NRS048/ArenaTimer/Print Files and Cad/Housing/Large Printer/Lenses/bottom_right.stl

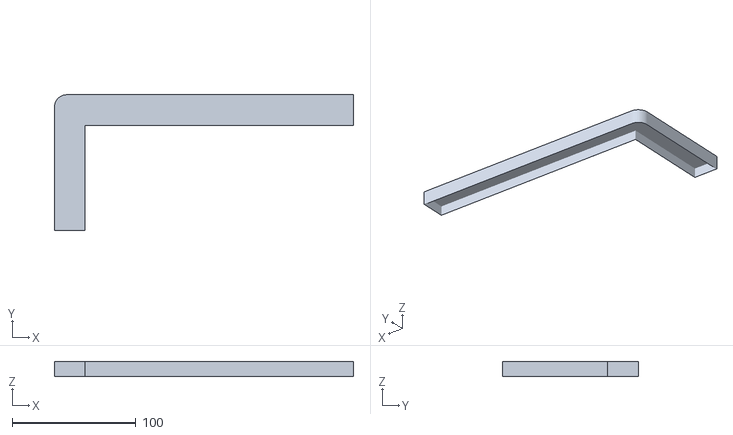
[picture p19: CAD file, 2026-07-04]
Print Files and Cad/Housing/Large Printer/Lenses/bottom_right.stl
242.1 x 109.8 x 12.5
