NRS048/ArenaTimer/Print Files and Cad/Housing/Small Printer/Bottom_right.stl

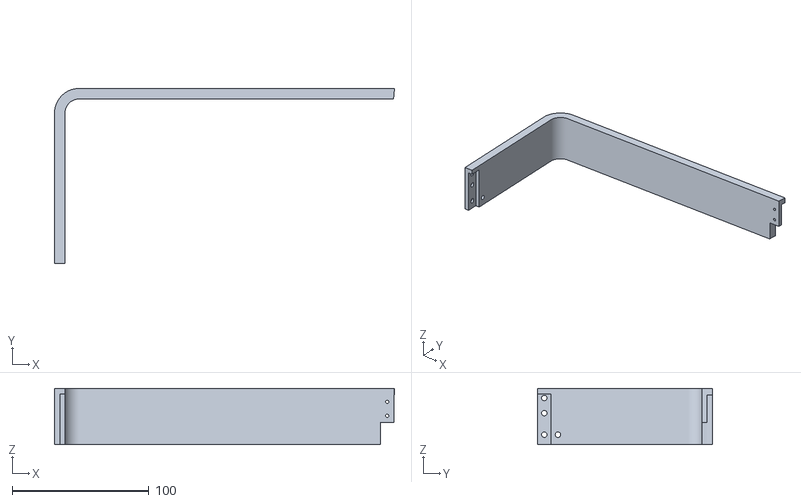
[picture p20: CAD file, 2026-07-04]
Print Files and Cad/Housing/Small Printer/Bottom_right.stl
248.6 x 128.0 x 41.0
