NRS048/ArenaTimer/Print Files and Cad/Remotes/Driver Ready/Driver Ready Remote v2_Driver Ready Remote v2_Body34.stl

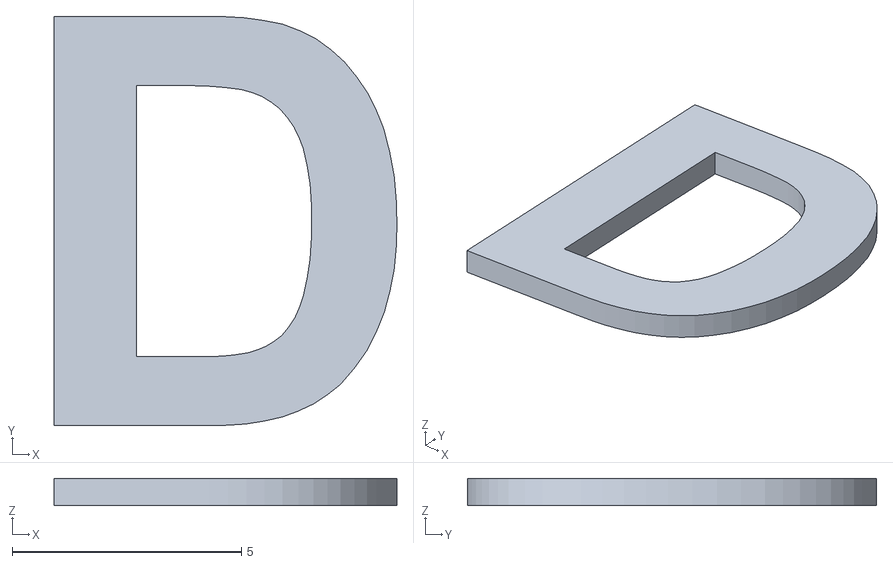
[picture p21: CAD file, 2026-07-04]
Print Files and Cad/Remotes/Driver Ready/Driver Ready Remote v2_Driver Ready Remote v2_Body34.stl
7.48 x 8.93 x 0.6
