NRS048/ArenaTimer/Print Files and Cad/Housing/Small Printer/Bottom_left.stl

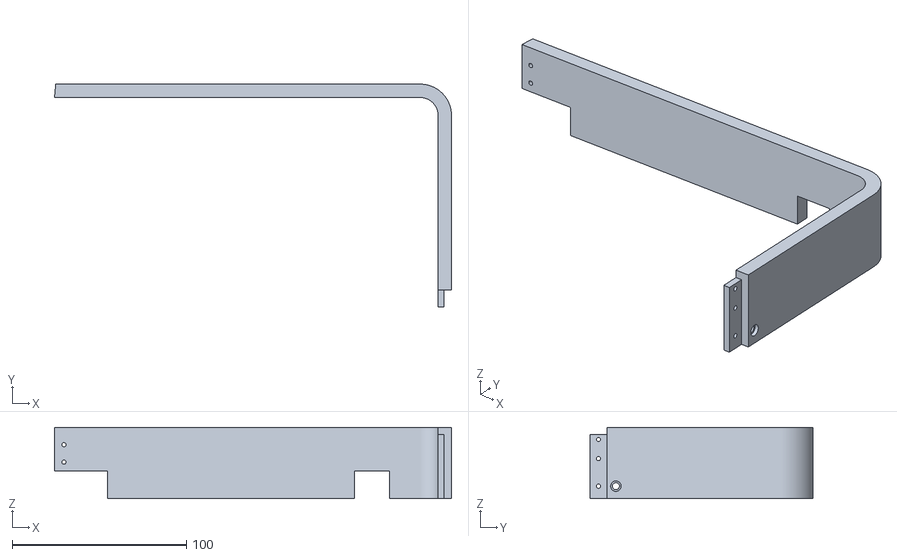
[picture p22: CAD file, 2026-07-04]
Print Files and Cad/Housing/Small Printer/Bottom_left.stl
227.7 x 127.8 x 41.0
