NRS048/ArenaTimer/Print Files and Cad/Housing/Small Printer/Lenses/seg_b.stl

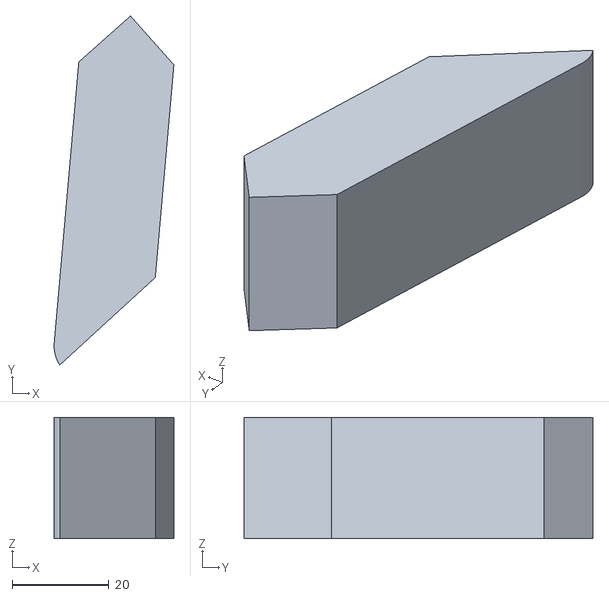
[picture p23: CAD file, 2026-07-04]
Print Files and Cad/Housing/Small Printer/Lenses/seg_b.stl
24.7 x 72.0 x 25.0
