NRS048/ArenaTimer/Print Files and Cad/Remotes/Driver Ready/Driver Ready Remote v2_Driver Ready Remote v2_Body25.stl

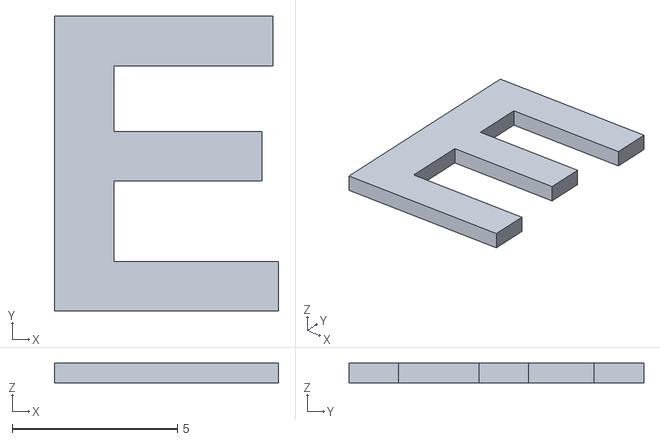
[picture p24: CAD file, 2026-07-04]
Print Files and Cad/Remotes/Driver Ready/Driver Ready Remote v2_Driver Ready Remote v2_Body25.stl
6.79 x 8.93 x 0.6
