NRS048/ArenaTimer/Print Files and Cad/Housing/Small Printer/Lenses/Top_right_lens.stl

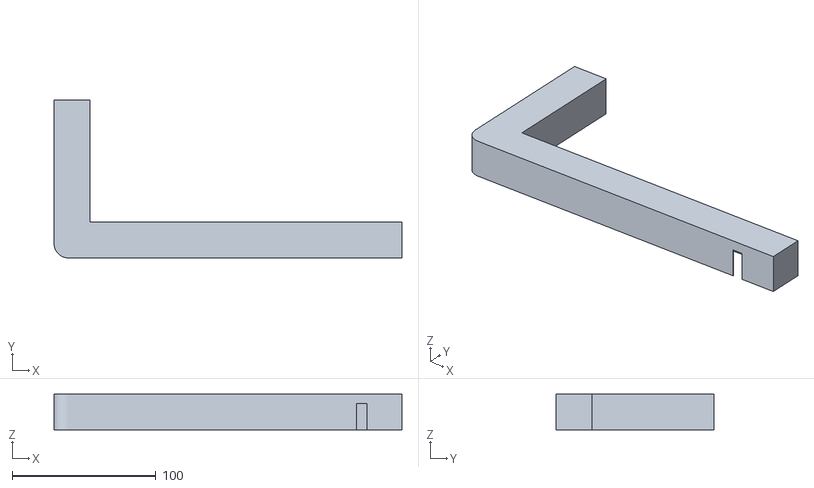
[picture p25: CAD file, 2026-07-04]
Print Files and Cad/Housing/Small Printer/Lenses/Top_right_lens.stl
242.2 x 109.9 x 25.0
