NRS048/ArenaTimer/Print Files and Cad/Housing/Small Printer/Top_left.stl

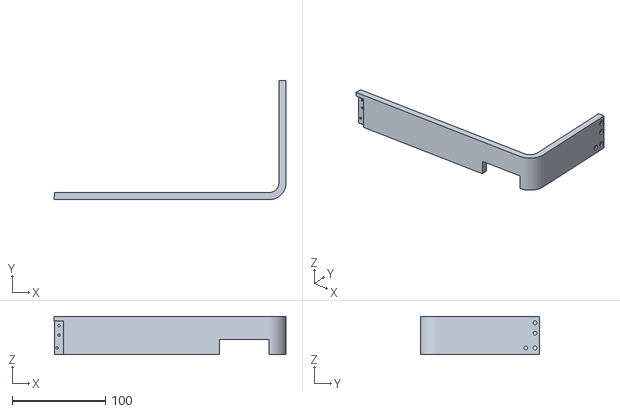
[picture p26: CAD file, 2026-07-04]
Print Files and Cad/Housing/Small Printer/Top_left.stl
248.6 x 128.0 x 41.0
