NRS048/ArenaTimer/Print Files and Cad/Remotes/Driver Ready/Driver Ready Remote v2_Driver Ready Remote v2_Body20.stl

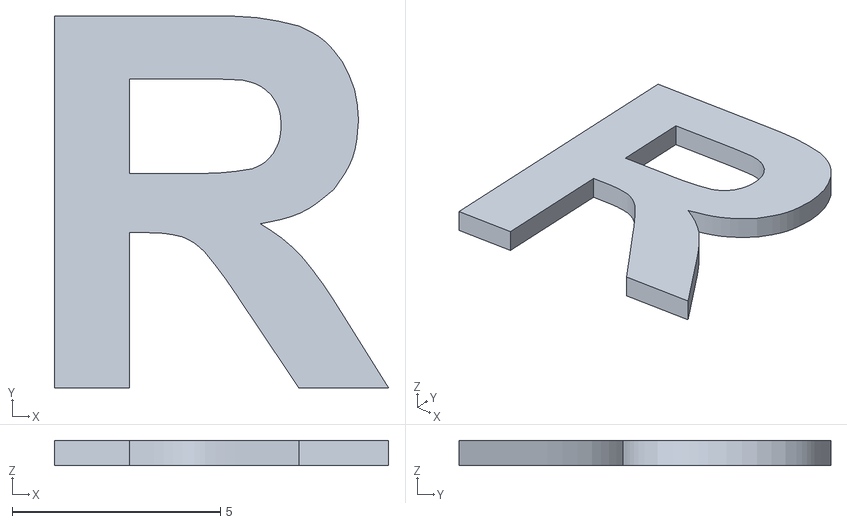
[picture p28: CAD file, 2026-07-04]
Print Files and Cad/Remotes/Driver Ready/Driver Ready Remote v2_Driver Ready Remote v2_Body20.stl
8.03 x 8.93 x 0.6
