NRS048/ArenaTimer/Print Files and Cad/Housing/Large Printer/Lenses/seg_f.stl

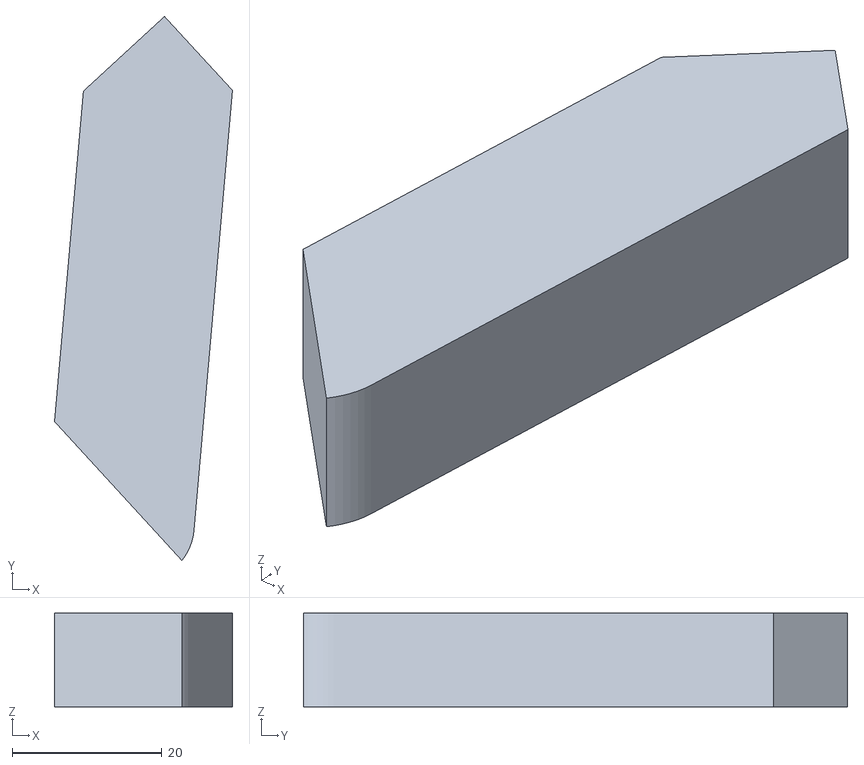
[picture p29: CAD file, 2026-07-04]
Print Files and Cad/Housing/Large Printer/Lenses/seg_f.stl
23.7 x 72.6 x 12.5
