NRS048/ArenaTimer/Print Files and Cad/Housing/Small Printer/Lenses/seg_g.stl

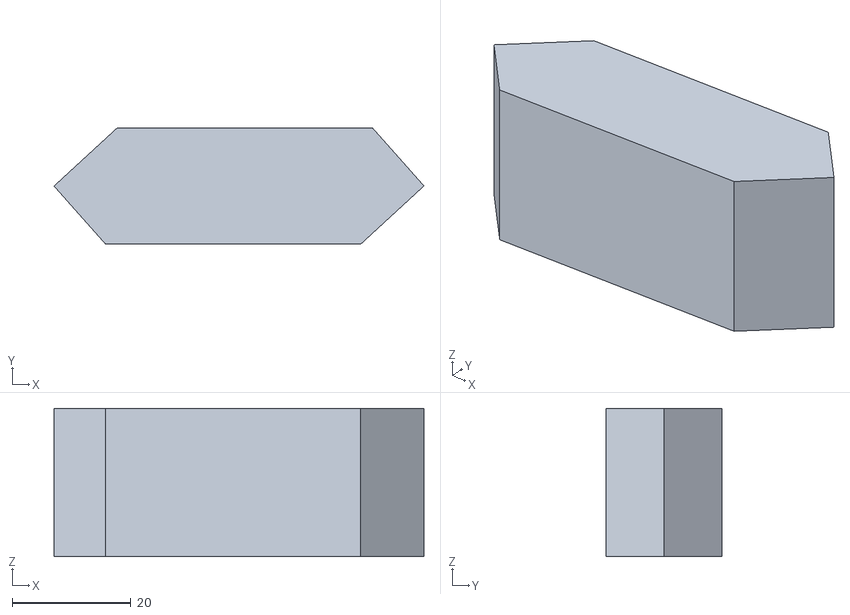
[picture p30: CAD file, 2026-07-04]
Print Files and Cad/Housing/Small Printer/Lenses/seg_g.stl
62.4 x 19.6 x 25.0
