NRS048/ArenaTimer/Print Files and Cad/Remotes/Controller/Timer Remote v22_Timer Remote v22_Body34.stl

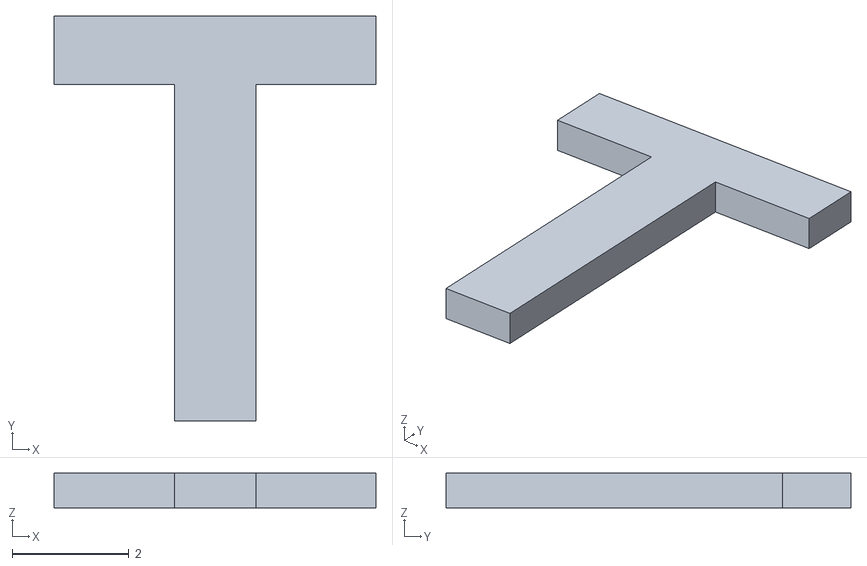
[picture p31: CAD file, 2026-07-20]
Print Files and Cad/Remotes/Controller/Timer Remote v22_Timer Remote v22_Body34.stl
5.52 x 6.94 x 0.6
