NRS048/ArenaTimer/Print Files and Cad/Remotes/Driver Ready/Driver Ready Remote v2_Driver Ready Remote v2_housing.stl

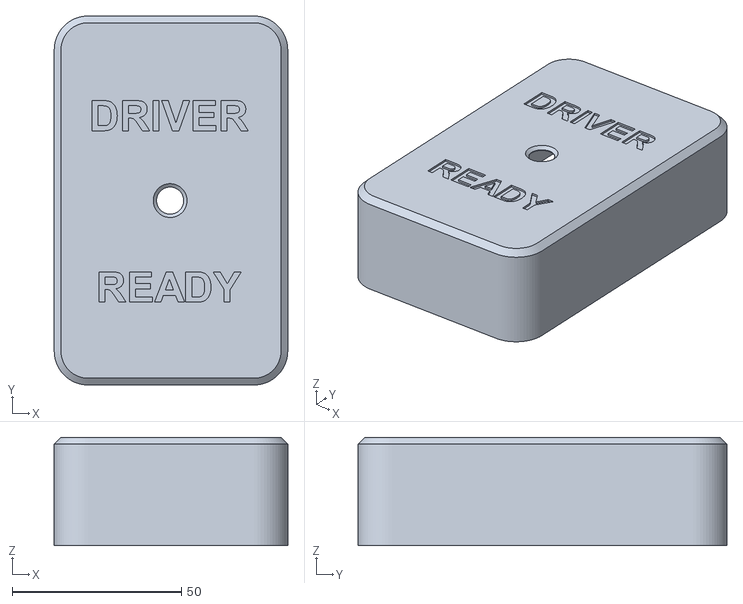
[picture p32: CAD file, 2026-07-04]
Print Files and Cad/Remotes/Driver Ready/Driver Ready Remote v2_Driver Ready Remote v2_housing.stl
69.0 x 109.0 x 32.0
