NRS048/ArenaTimer/Print Files and Cad/Housing/Small Printer/Lenses/seg_f.stl

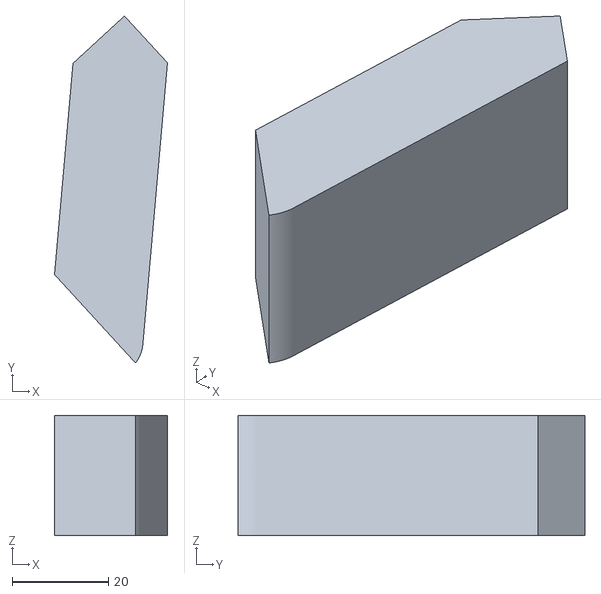
[picture p34: CAD file, 2026-07-04]
Print Files and Cad/Housing/Small Printer/Lenses/seg_f.stl
23.5 x 72.3 x 25.0
