NRS048/ArenaTimer/Print Files and Cad/Remotes/Controller/Timer Remote v22_Timer Remote v22_Body25.stl

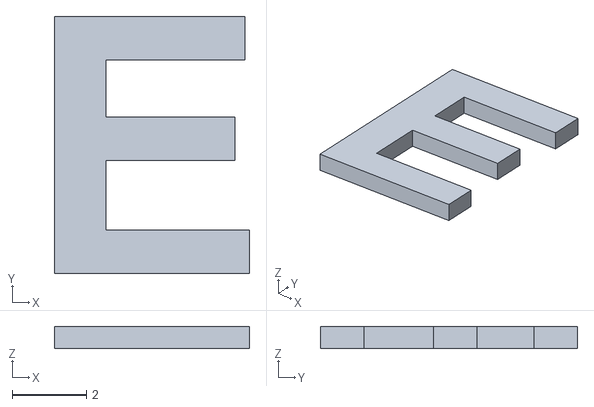
[picture p35: CAD file, 2026-07-20]
Print Files and Cad/Remotes/Controller/Timer Remote v22_Timer Remote v22_Body25.stl
5.28 x 6.94 x 0.6
