NRS048/ArenaTimer/Print Files and Cad/Housing/Large Printer/Lenses/seg_g.stl

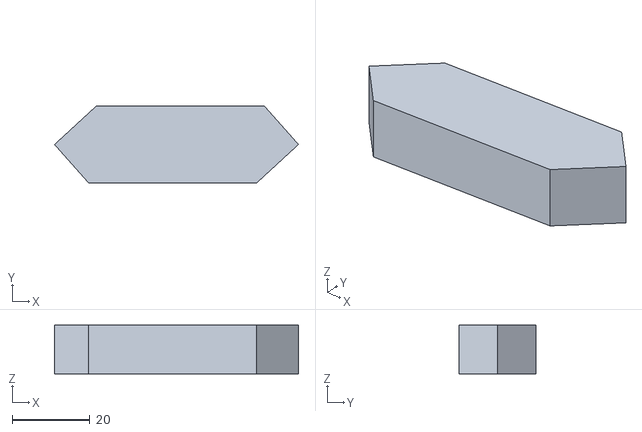
[picture p37: CAD file, 2026-07-04]
Print Files and Cad/Housing/Large Printer/Lenses/seg_g.stl
62.6 x 19.8 x 12.5
