NRS048/ArenaTimer/Print Files and Cad/Remotes/Controller/Timer Remote v22_Timer Remote v22_Body11.stl

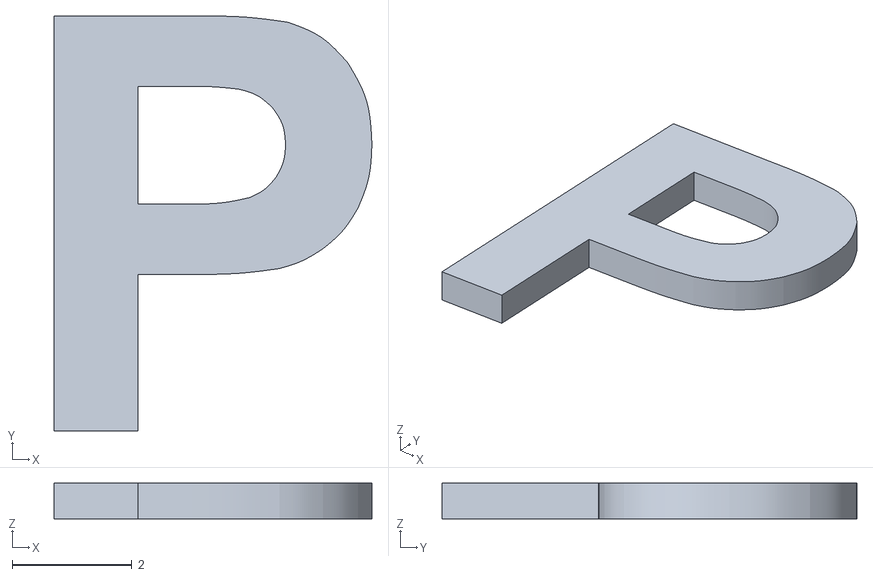
[picture p38: CAD file, 2026-07-20]
Print Files and Cad/Remotes/Controller/Timer Remote v22_Timer Remote v22_Body11.stl
5.32 x 6.94 x 0.6
