NRS048/ArenaTimer/Print Files and Cad/Remotes/Controller/Timer Remote v22_Timer Remote v22_Body26.stl

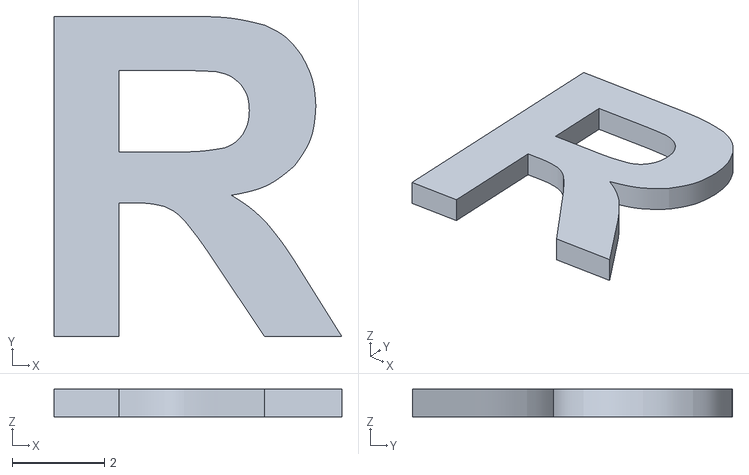
[picture p39: CAD file, 2026-07-20]
Print Files and Cad/Remotes/Controller/Timer Remote v22_Timer Remote v22_Body26.stl
6.24 x 6.94 x 0.6
