NRS048/ArenaTimer/Print Files and Cad/Housing/Small Printer/Lenses/seg_e.stl

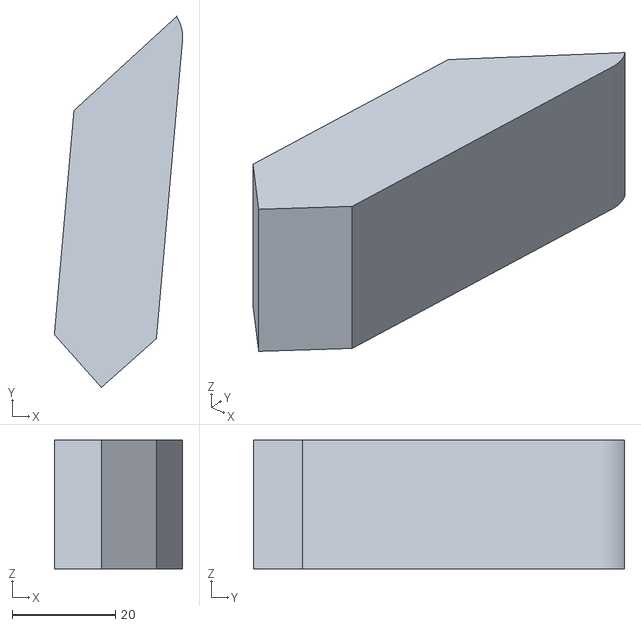
[picture p40: CAD file, 2026-07-04]
Print Files and Cad/Housing/Small Printer/Lenses/seg_e.stl
24.9 x 72.0 x 25.0
