NRS048/ArenaTimer/Print Files and Cad/Remotes/Controller/Timer Remote v22_Timer Remote v22_Body10.stl

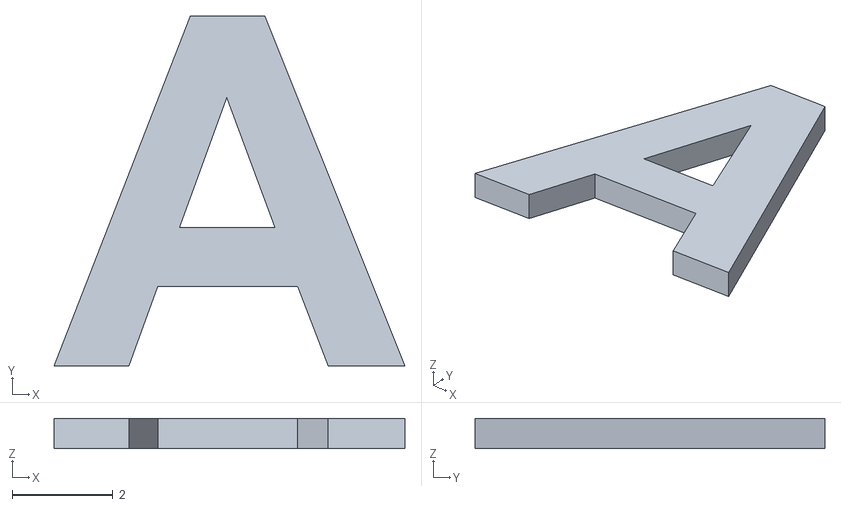
[picture p42: CAD file, 2026-07-04]
Print Files and Cad/Remotes/Controller/Timer Remote v22_Timer Remote v22_Body10.stl
6.97 x 6.94 x 0.6
