NRS048/ArenaTimer/Print Files and Cad/Remotes/Controller/Timer Remote v22_Timer Remote v22_Body23.stl

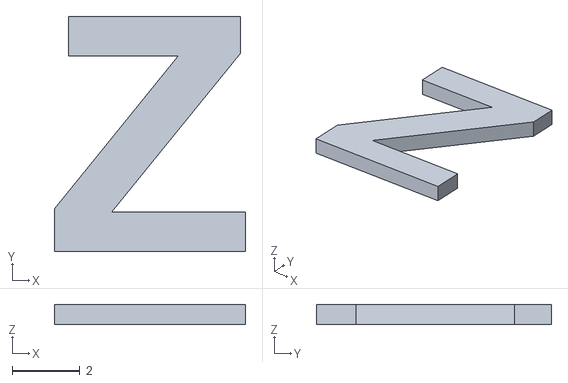
[picture p43: CAD file, 2026-07-04]
Print Files and Cad/Remotes/Controller/Timer Remote v22_Timer Remote v22_Body23.stl
5.64 x 6.94 x 0.6
