NRS048/ArenaTimer/Print Files and Cad/Remotes/Controller/Timer Remote v22_Timer Remote v22_Body18.stl

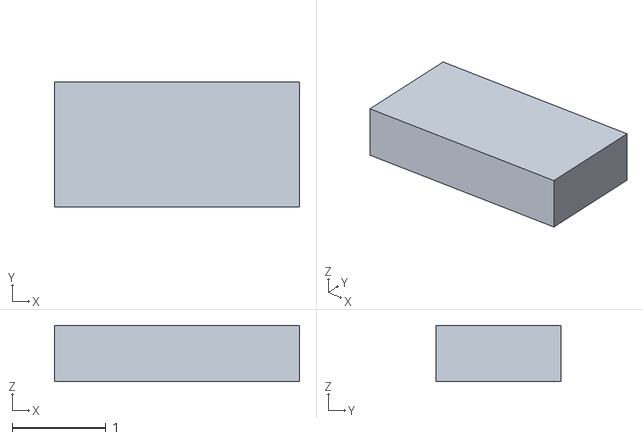
[picture p44: CAD file, 2026-07-04]
Print Files and Cad/Remotes/Controller/Timer Remote v22_Timer Remote v22_Body18.stl
2.61 x 1.33 x 0.6
