NRS048/ArenaTimer/Print Files and Cad/Remotes/Controller/Timer Remote v22_Timer Remote v22_Body21.stl

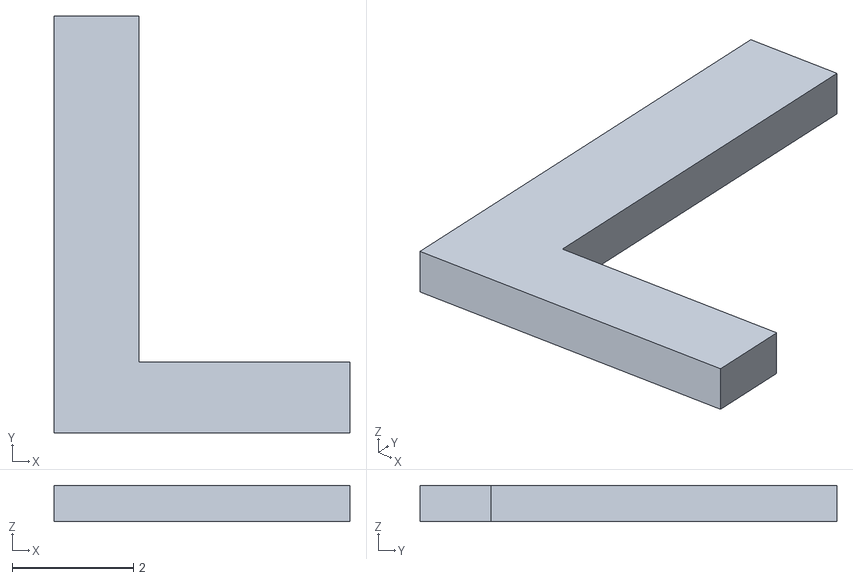
[picture p45: CAD file, 2026-07-04]
Print Files and Cad/Remotes/Controller/Timer Remote v22_Timer Remote v22_Body21.stl
4.89 x 6.89 x 0.6
